tebl/RC6802-Microchicken/gallery/2019-09-19 11.49.34.jpg

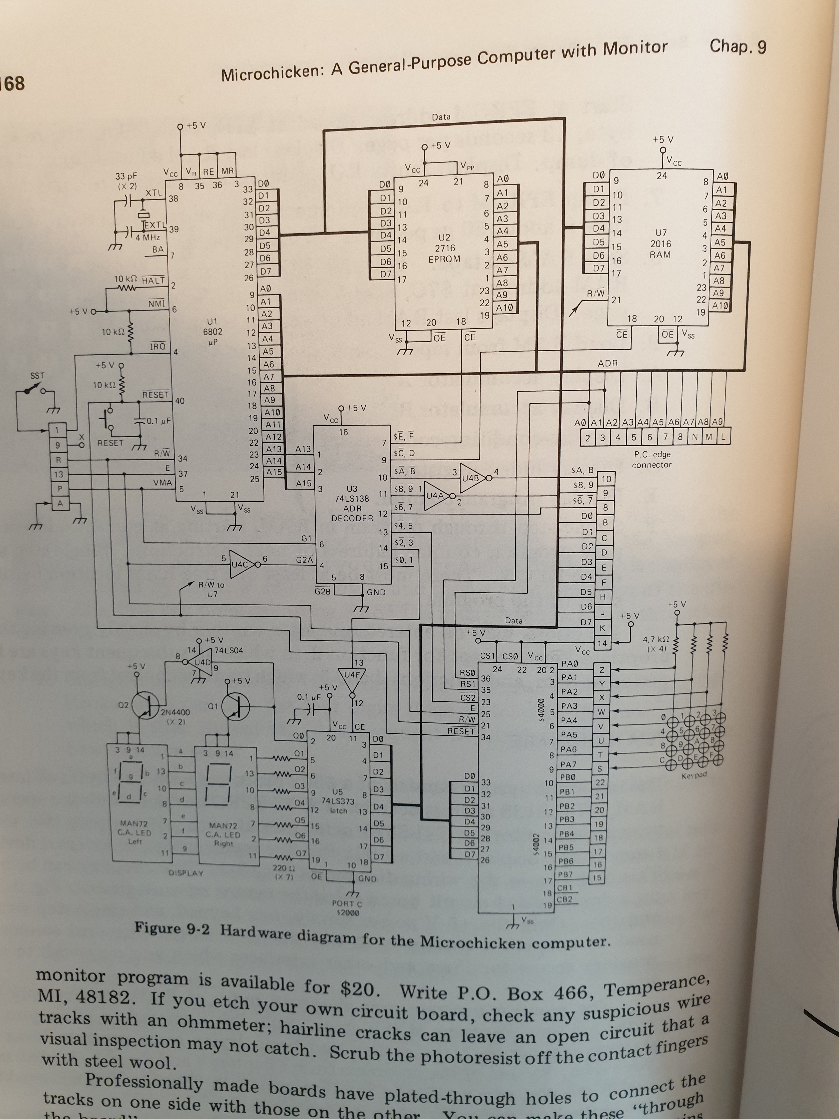
gallery/2019-09-19 11.49.34.jpg
