tebl/RC6802-Microchicken/RC6802 CPU/gallery/2019-11-13 23.02.54.jpg

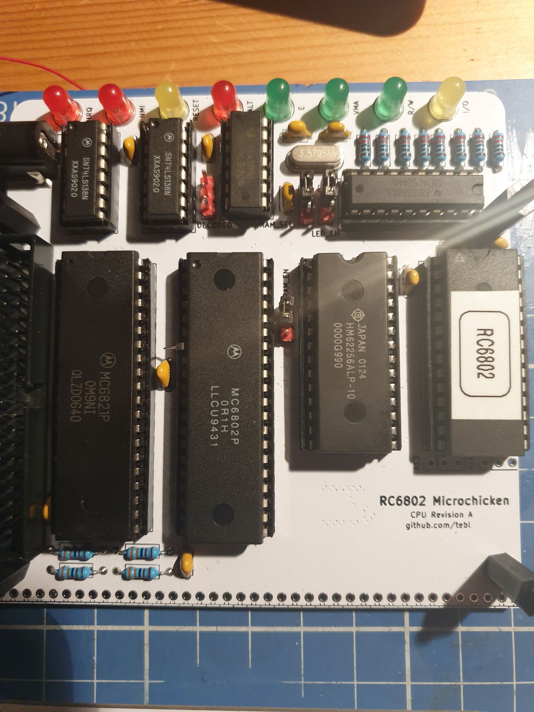
RC6802 CPU/gallery/2019-11-13 23.02.54.jpg
