tebl/RC6802-Microchicken/RC6802 Serial Chicken/gallery/RC6802 Serial Chicken #2.png

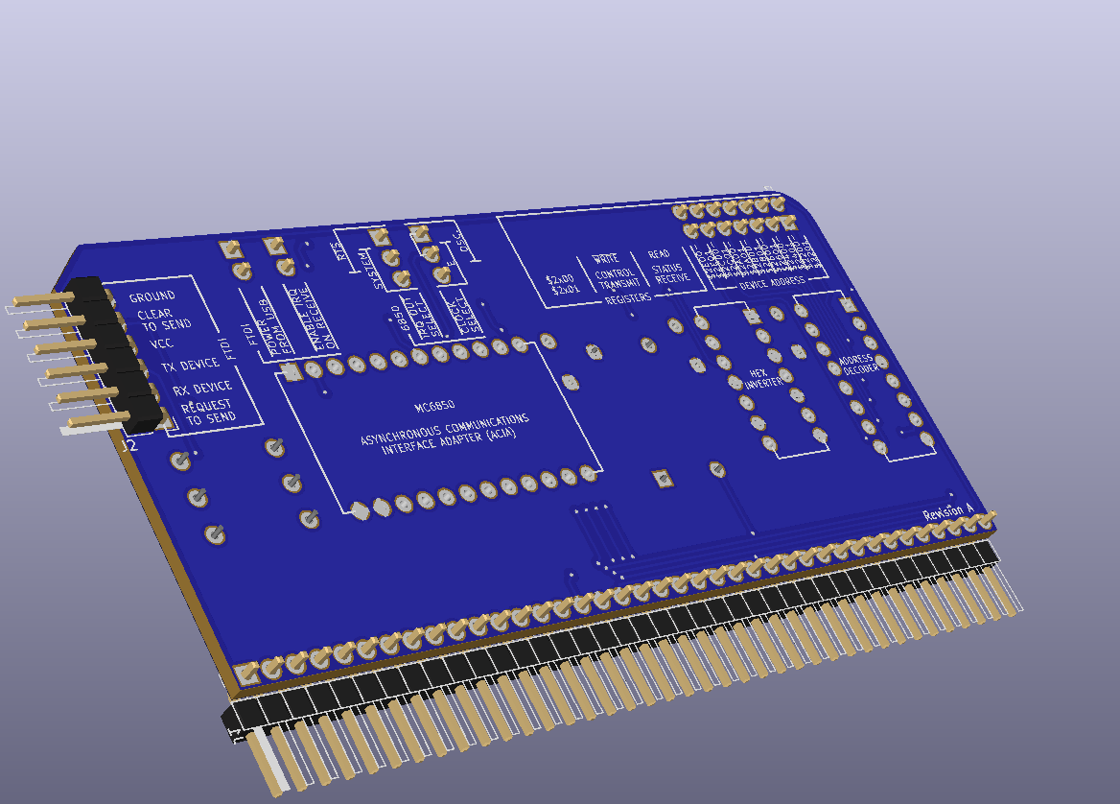
RC6802 Serial Chicken/gallery/RC6802 Serial Chicken #2.png
