tebl/RC6802-Microchicken/RC6802 UI/gallery/RC6802 UI #1.png

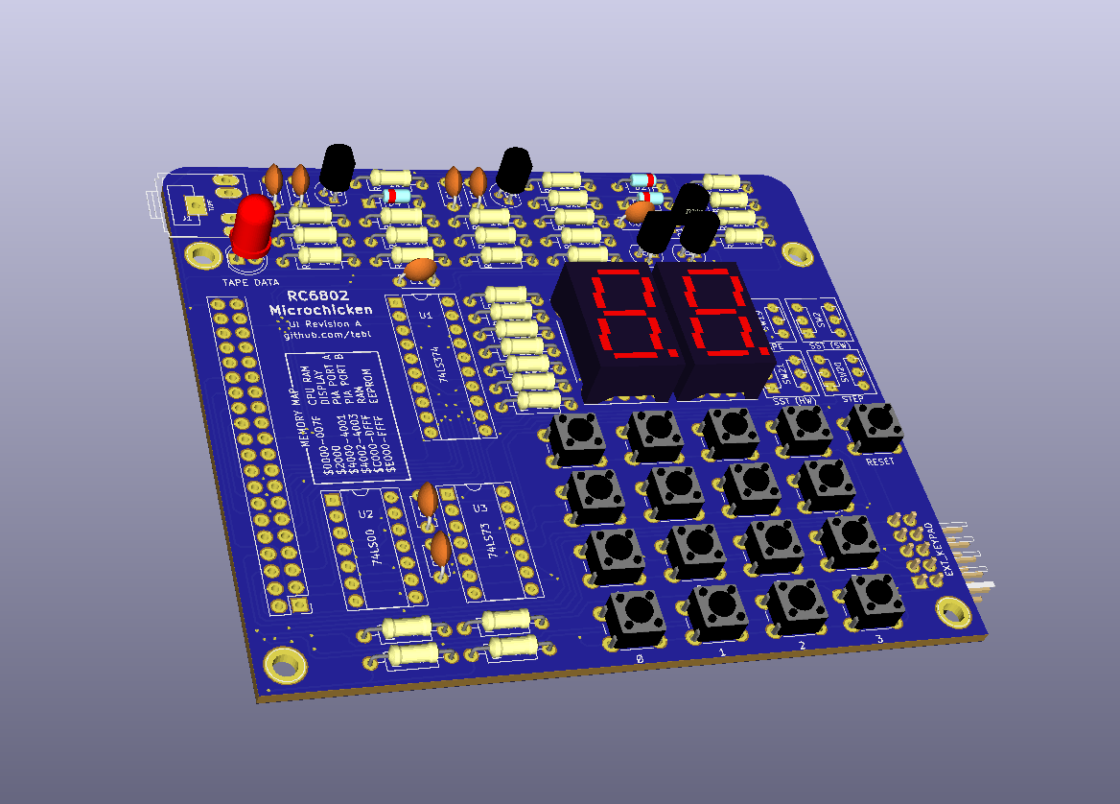
RC6802 UI/gallery/RC6802 UI #1.png
